robertrico/project_byte_hamr/docs/blog/multiverse/gliders.png

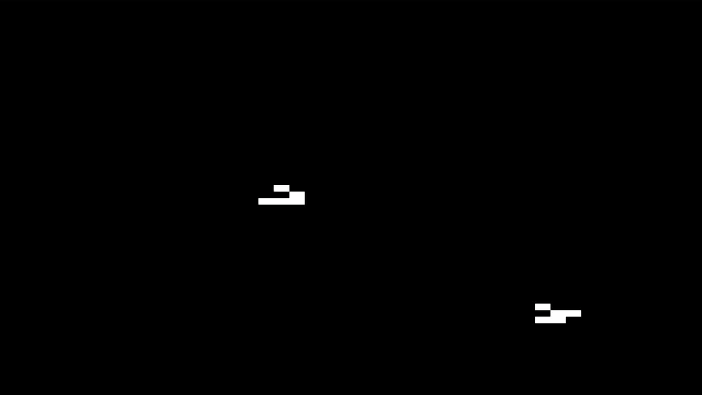
docs/blog/multiverse/gliders.png
