robertrico/project_byte_hamr/docs/blog/multiverse/hero.png

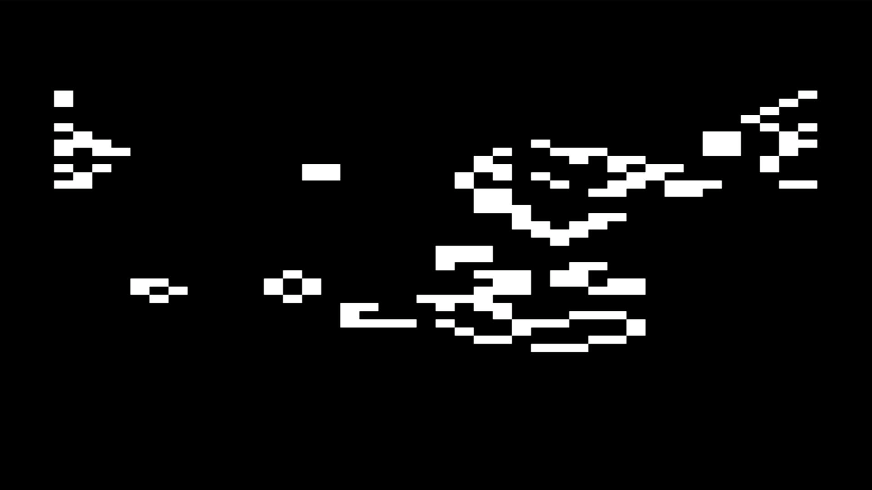
docs/blog/multiverse/hero.png
