robertrico/project_byte_hamr/docs/blog/multiverse/rpentomino-ash.png

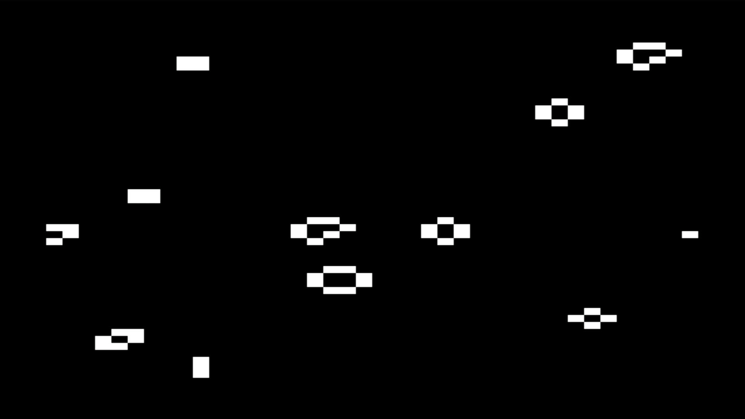
docs/blog/multiverse/rpentomino-ash.png
