robertrico/project_byte_hamr/docs/blog/multiverse/soup-growing.png

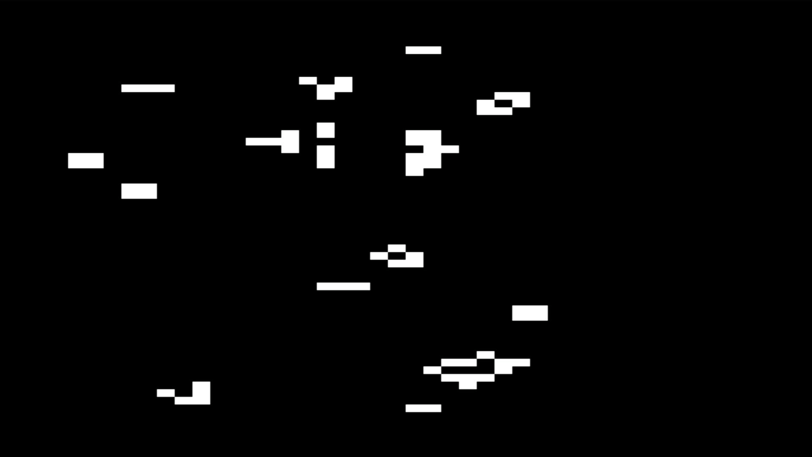
docs/blog/multiverse/soup-growing.png
