robertrico/project_byte_hamr/docs/Logic Hamr/Screenshot 2026-02-04 16-10-01.png

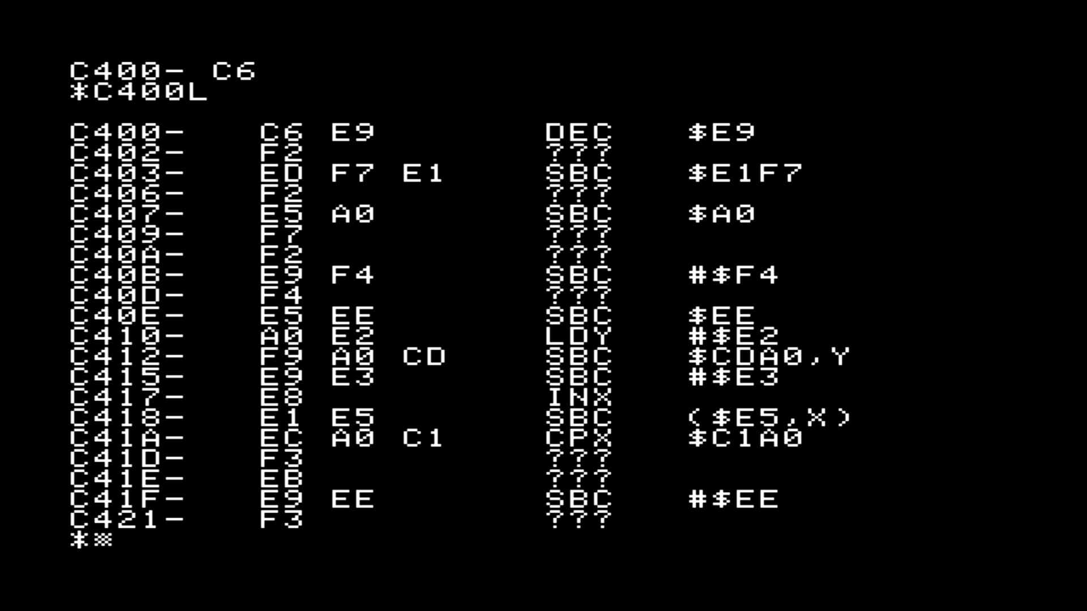
docs/Logic Hamr/Screenshot 2026-02-04 16-10-01.png
