robertrico/project_byte_hamr/docs/Logic Hamr/Screenshot 2026-02-04 16-26-15.png

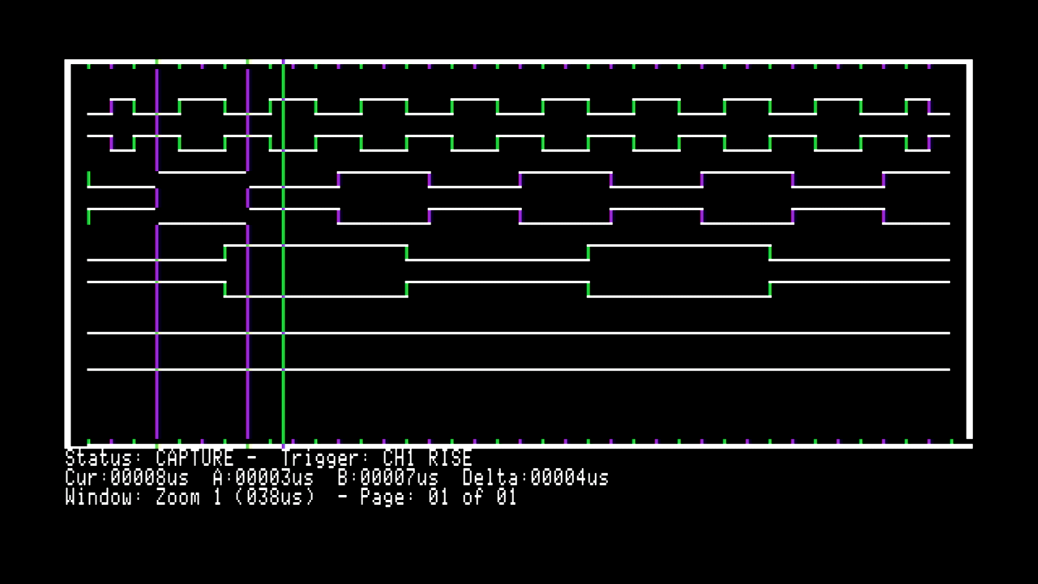
docs/Logic Hamr/Screenshot 2026-02-04 16-26-15.png
