robertrico/project_byte_hamr/docs/Logic Hamr/Screenshot 2026-02-04 16-27-03.png

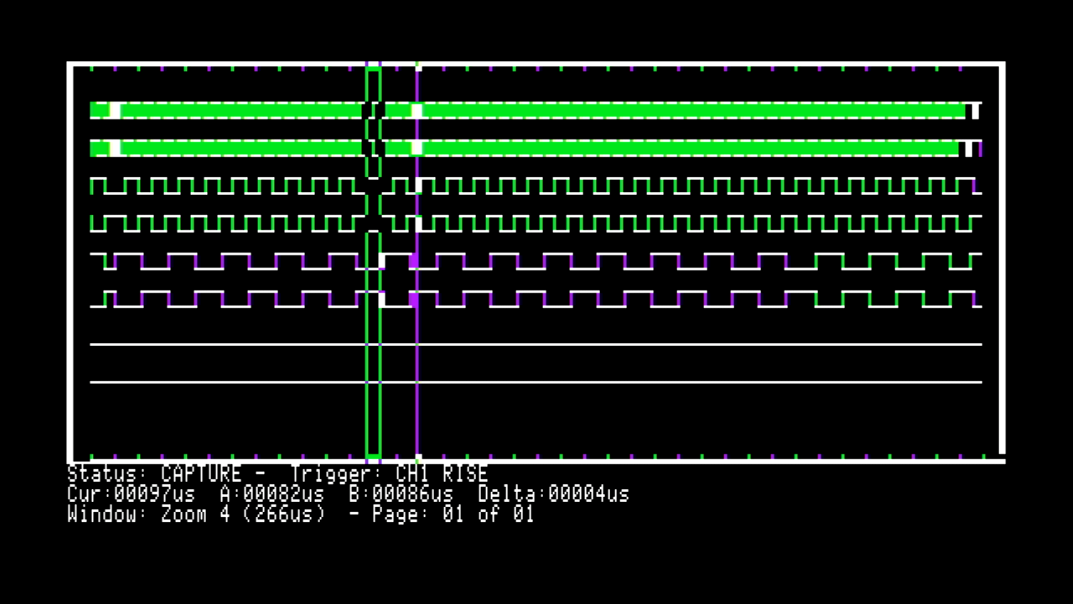
docs/Logic Hamr/Screenshot 2026-02-04 16-27-03.png
