robertrico/project_byte_hamr/docs/Logic Hamr/Screenshot 2026-02-04 17-45-49.png

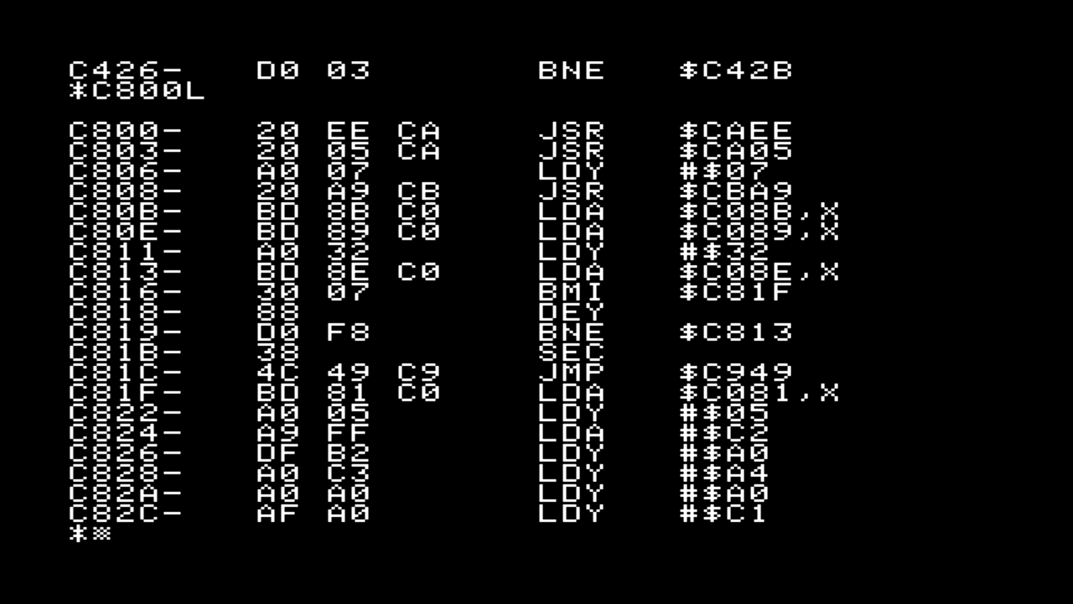
docs/Logic Hamr/Screenshot 2026-02-04 17-45-49.png
