robertrico/project_byte_hamr/docs/Logic Hamr/Screenshot 2026-02-07 22-06-17.png

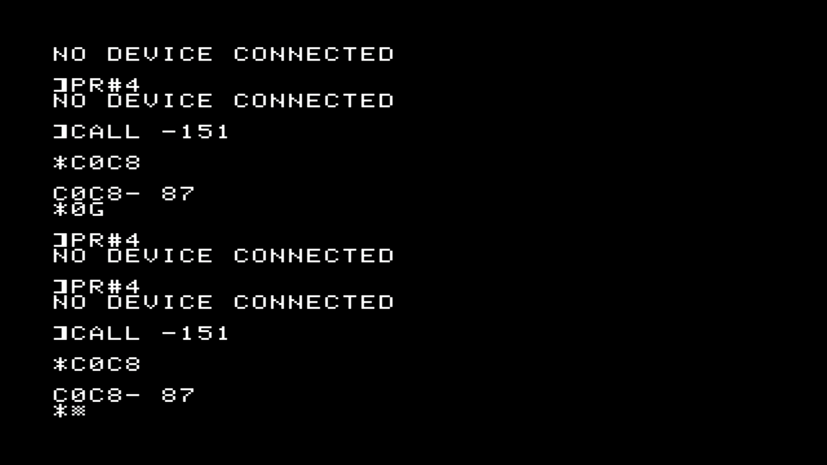
docs/Logic Hamr/Screenshot 2026-02-07 22-06-17.png
