robertrico/project_byte_hamr/docs/Logic Hamr/Screenshot 2026-02-08 11-18-13.png

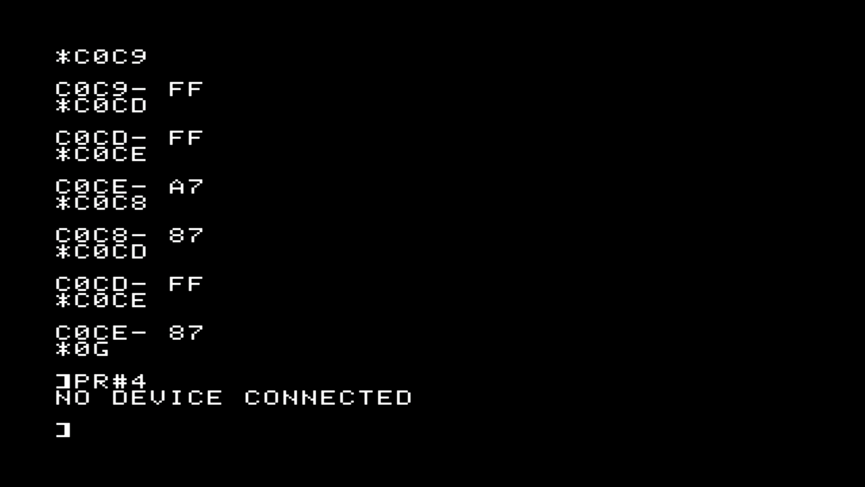
docs/Logic Hamr/Screenshot 2026-02-08 11-18-13.png
