robertrico/project_byte_hamr/docs/project_byte_hamr.jpg

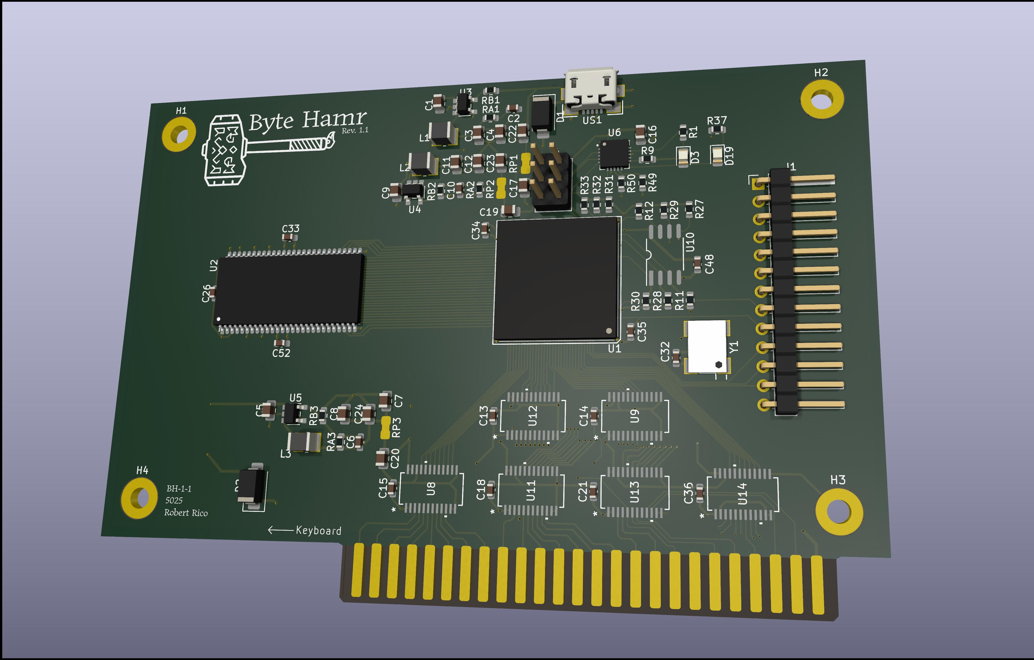
docs/project_byte_hamr.jpg
