robertrico/project_byte_hamr/docs/project_byte_hamr_back.jpg

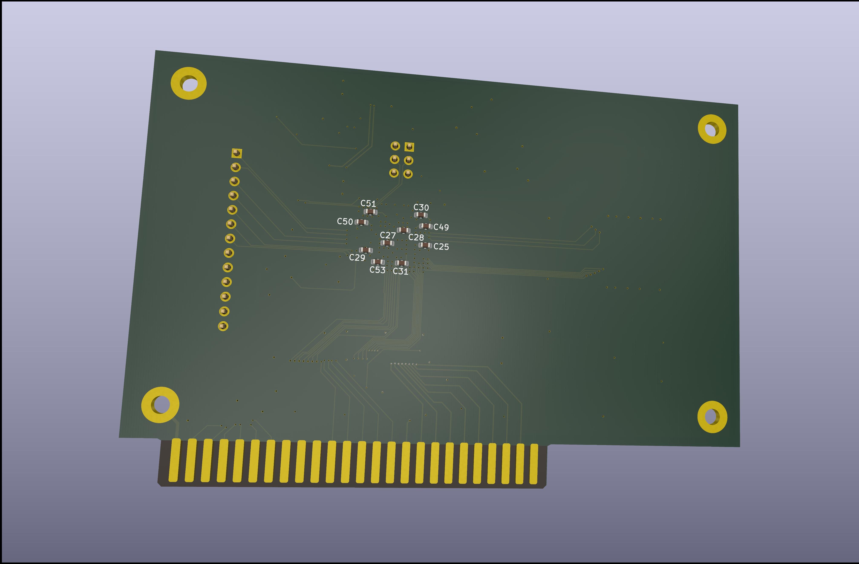
docs/project_byte_hamr_back.jpg
