robertrico/project_byte_hamr/docs/Smart Hamr/Screenshot 2026-03-02 16-48-08.png

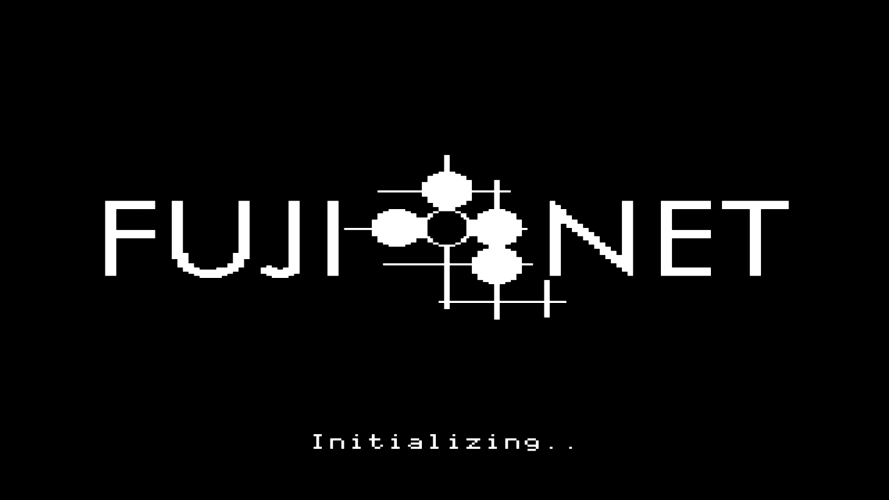
docs/Smart Hamr/Screenshot 2026-03-02 16-48-08.png
