robertrico/project_byte_hamr/docs/Smart Hamr/Screenshot 2026-03-02 16-52-01.png

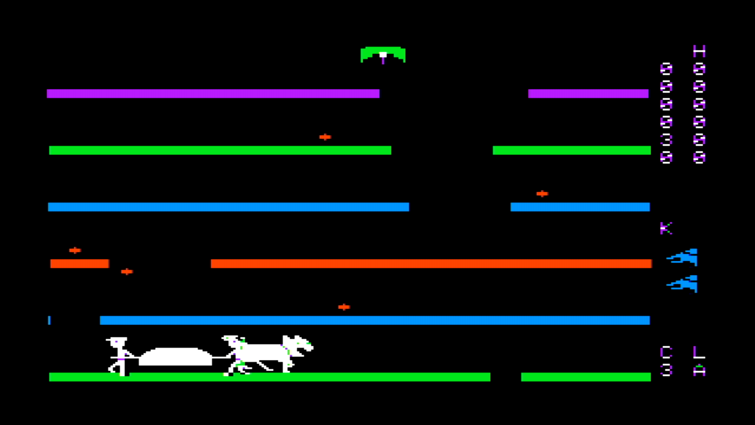
docs/Smart Hamr/Screenshot 2026-03-02 16-52-01.png
