robertrico/project_byte_hamr/docs/Smart Hamr/Screenshot 2026-03-02 16-53-50.png

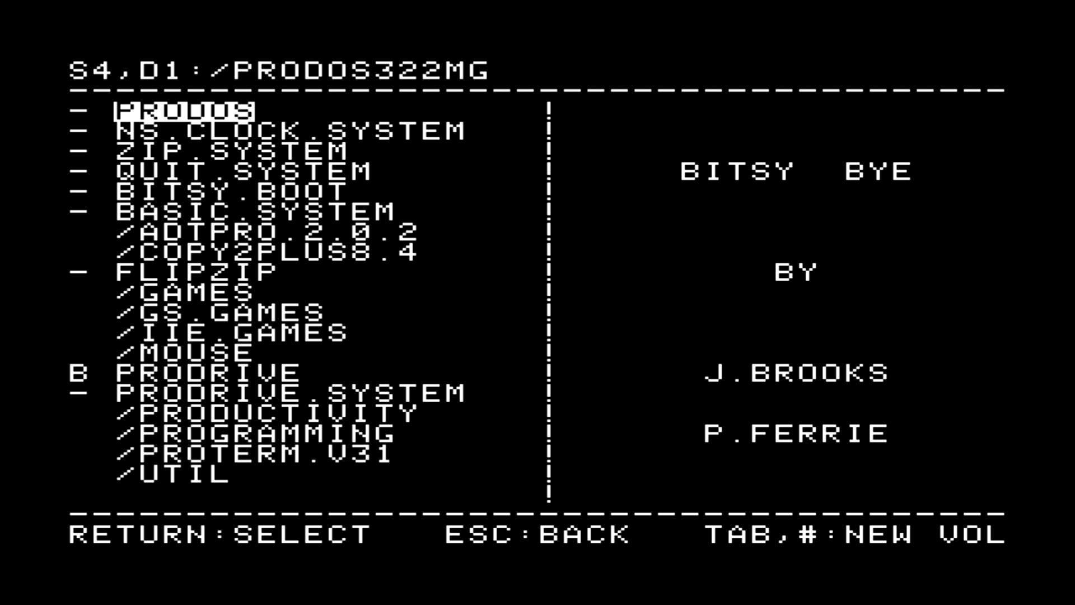
docs/Smart Hamr/Screenshot 2026-03-02 16-53-50.png
