robertrico/project_byte_hamr/docs/Smart Hamr/Screenshot 2026-03-02 17-01-03.png

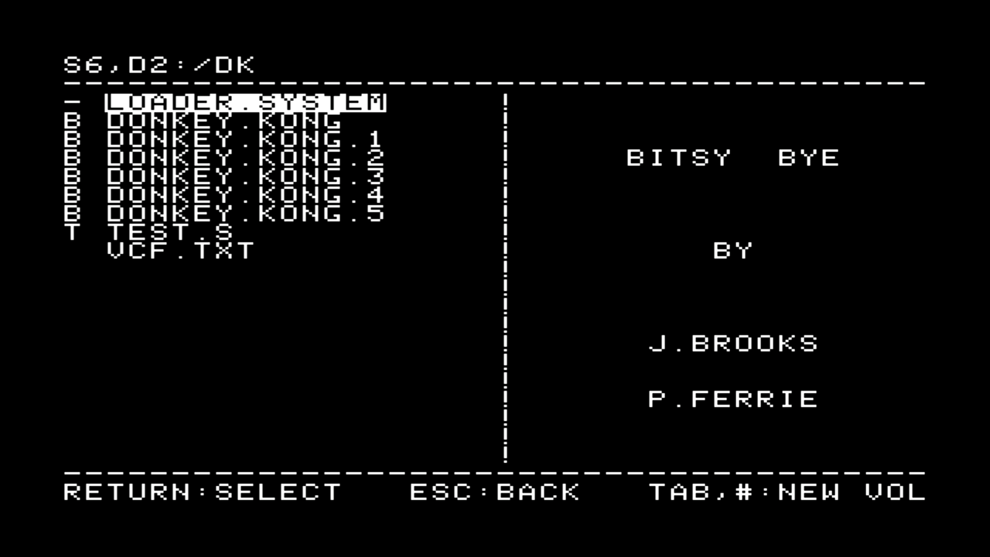
docs/Smart Hamr/Screenshot 2026-03-02 17-01-03.png
