robertrico/project_byte_hamr/docs/Smart Hamr/Screenshot 2026-03-02 17-02-29.png

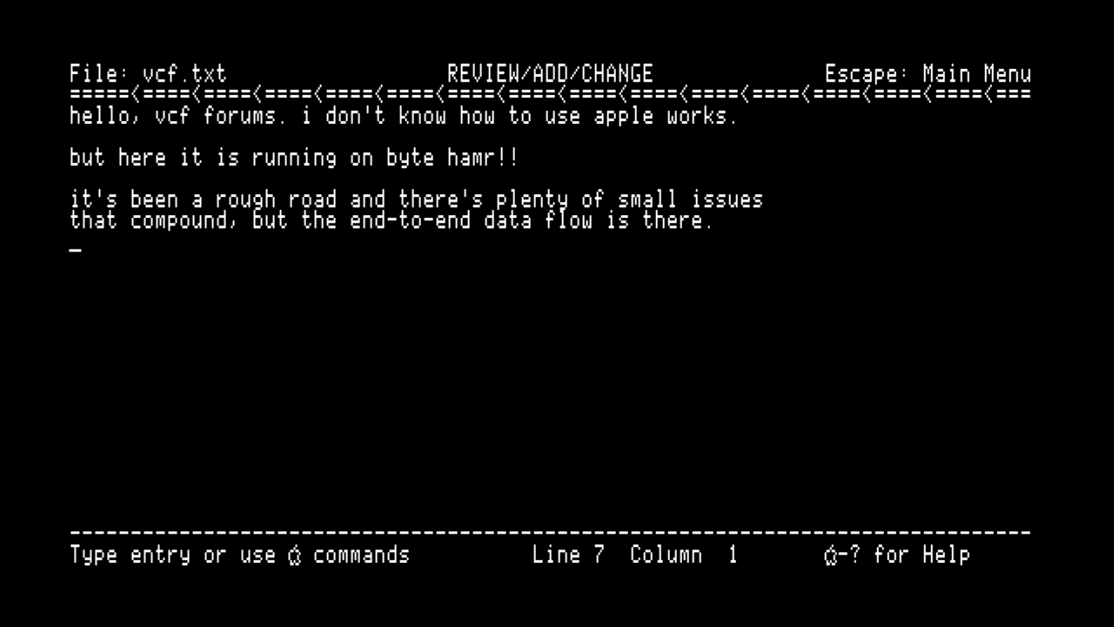
docs/Smart Hamr/Screenshot 2026-03-02 17-02-29.png
