robertrico/project_byte_hamr/docs/timing_chart.jpg

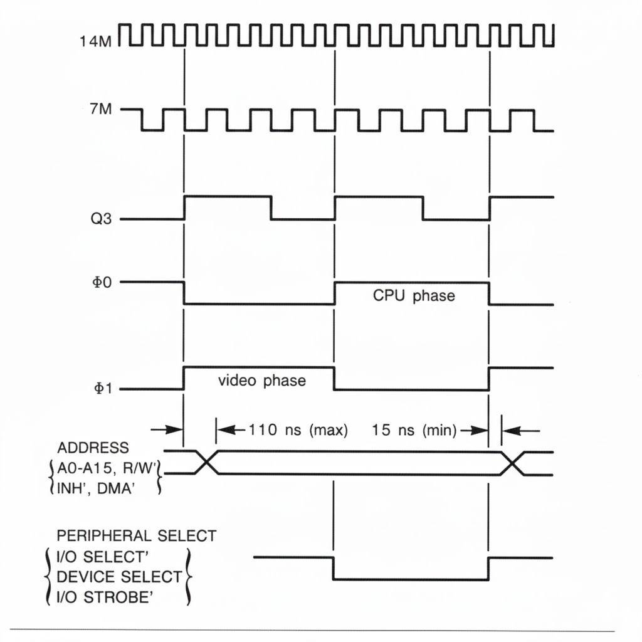
docs/timing_chart.jpg
