robertrico/project_byte_hamr/gateware/rev2/block_hamr/hamr_rom.asm

; =============================================================================
; hamr_rom.asm — Byte Hamr ProDOS/SmartPort block device ROM
; =============================================================================
; Talks to FPGA register file for block reads/writes.
;
; Register interface ($C0n0 + slot*16):
;   REG_CMD   ($C080,X): Read = STATUS, Write = COMMAND
;     STATUS read:  {ready, error, 5'b0, boot_done}
;     COMMAND write: $01 = READ_BLOCK, $02 = WRITE_BLOCK
;   REG_DATA  ($C081,X): Read/Write data, auto-increments
;   REG_BLK_LO ($C082,X): Block number low byte
;   REG_BLK_HI ($C083,X): Block number high byte
;
; ROM memory map (as seen by boot_rom.v):
;   $400-$4FF: Slot ROM ($Cn00-$CnFF)
;   $800-$FFF: Shared ROM ($C800-$CFFF)
;
; Assembled for slot 4, but slot number only matters for the $Cn
; page — the $C800 code uses dynamic slot detection.
; =============================================================================

	cpu	65c02

; ---- Zero page temporaries (safe range $40-$5B) ----
slot		equ	$58	; slot number (1-7)
buf_ptr		equ	$44	; ProDOS buffer pointer (lo/hi)
buf_ptr_h	equ	$45

; ---- ProDOS command block ($42-$47) ----
prodos_command	equ	$42
prodos_unit	equ	$43
prodos_buffer	equ	$44
prodos_block	equ	$46
prodos_block_h	equ	$47

; ---- Screen holes (per-slot, indexed by slot number) ----
sh_prodos_flag	equ	$0478	; MSB=1 for ProDOS, 0 for SmartPort
sh_magic1	equ	$06f8	; $A5 if initialized
sh_magic2	equ	$0778	; $5A if initialized
sh_unit_count	equ	$07f8	; number of units
sh_05f8		equ	$05f8	; SmartPort return addr lo
sh_0678		equ	$0678	; SmartPort return addr hi

; ---- Global screen holes ----
gh_shared_slot	equ	$07f8	; $Cn for active $C800 ROM

; ---- Apple II ROM / Monitor ----
rom_dis		equ	$cfff	; accessing this deactivates $C800 ROMs

; ---- I/O register base addresses (indexed by slot*16) ----
REG_CMD		equ	$c080	; STATUS read / COMMAND write
REG_DATA	equ	$c081	; DATA (auto-increment)
REG_BLK_LO	equ	$c082	; Block number low
REG_BLK_HI	equ	$c083	; Block number high

; ---- ProDOS error codes ----
ERR_NONE	equ	$00
ERR_BAD_CMD	equ	$01
ERR_IO		equ	$27
ERR_NO_DRIVE	equ	$28
ERR_NO_WRITE	equ	$2b
ERR_BAD_BLOCK	equ	$2d

; ---- Block count for .po image (280 blocks = $0118) ----
BLOCK_COUNT_LO	equ	$18	; 280 & $FF
BLOCK_COUNT_HI	equ	$01	; 280 >> 8

; ---- Commands ----
CMD_READ	equ	$01
CMD_WRITE	equ	$02


; =============================================================================
; Slot ROM: $C400-$C4FF (mapped to ROM $400-$4FF)
; =============================================================================
; ProDOS looks for: $Cn01=$20, $Cn03=$00, $Cn05=$03, $CnFF=entry_lo
; Boot entry is at $Cn00 with carry set (from boot scan)

	org	$c400

; ---- Boot/signature entry ($C400 = $Cn00) ----
	ldx	#$20		; $Cn01 = $20: block device
	ldx	#$00		; $Cn03 = $00: no specific type
	ldx	#$03		; $Cn05 = $03: "smart" device (supports STATUS)
	cmp	#$00		; $Cn07 = $00 (padding)
	bcs	cn14		; carry set = boot request

; ---- ProDOS entry ($C409 = $Cn09) ----
prodos_entry:
	sec
	bcs	cn0e

; ---- SmartPort entry ($C40B = $Cn0B) ----
smartport_entry:
	clc

; ---- Combined dispatch ($C40C = $Cn0E, after CLC/SEC) ----
cn0e:
	ldx	#$04		; slot 4
	ror	sh_prodos_flag,x
	clc			; clear carry for execute_command path

; ---- Combined boot/command entry ($C414 = $Cn14) ----
cn14:
	ldx	#$c4		; $C0 + slot
	stx	gh_shared_slot
	ldx	#$04		; slot number
	lda	rom_dis		; deactivate other $C800 ROMs
	jmp	shared_entry	; jump to $C800 space

; ---- Pad to $CnFB ----
	; (filler — rest of $Cn space available for future use)

	org	$c4fb

	fcb	$00		; $CnFB: SmartPort device type (0 = block device)
	fdb	$0000		; $CnFC-FD: block count (0 = requires STATUS call)
	fcb	$bf		; $CnFE: ProDOS characteristics
				;   bit 7: removable
				;   bit 5: support STATUS
				;   bit 4: support READ/WRITE
				;   bit 3: support FORMAT
				;   bit 0: support SmartPort
	fcb	prodos_entry & $ff  ; $CnFF: ProDOS entry point low byte


; =============================================================================
; Shared ROM: $C800-$CFFF (mapped to ROM $800-$FFF)
; =============================================================================

	org	$c800

; ---- Entry point from slot ROM ----
shared_entry:
	bcc	execute_command	; C=0: ProDOS/SmartPort command
	jmp	boot		; C=1: boot request

; ---- Command dispatcher ----
execute_command:
	cld
	stx	slot		; save slot number

	; Get slot*16 into X for register access
	jsr	get_slot_x

	lda	sh_prodos_flag-1,x	; wait — X is slot*16 here, not slot
	; Fix: need slot number for screen hole indexing
	; Screen holes are indexed by slot number, not slot*16

	; Reload slot number for screen hole access
	ldy	slot

	lda	sh_prodos_flag,y
	bmi	prodos_cmd	; MSB=1: ProDOS call

	; ---- SmartPort call ----
	; Pull return address from stack, read inline params
	pla
	sta	sh_05f8,y	; return addr lo
	clc
	adc	#$03		; skip cmd byte + param ptr
	tax
	pla
	sta	sh_0678,y	; return addr hi
	adc	#$00
	pha			; push adjusted return addr
	txa
	pha

	; Read SmartPort command byte and param list from inline data
	lda	sh_05f8,y
	sta	buf_ptr
	lda	sh_0678,y
	sta	buf_ptr_h

	ldy	#$01
	lda	(buf_ptr),y	; SmartPort command
	sta	prodos_command
	iny
	lda	(buf_ptr),y	; param list lo
	tax
	iny
	lda	(buf_ptr),y	; param list hi
	sta	buf_ptr_h
	stx	buf_ptr

	; Copy SmartPort params to ProDOS command block
	ldy	#$00
	lda	(buf_ptr),y	; param count (ignored for now)
	iny
	lda	(buf_ptr),y	; unit number
	sta	prodos_unit
	iny
	lda	(buf_ptr),y	; buffer lo
	sta	prodos_buffer
	iny
	lda	(buf_ptr),y	; buffer hi
	sta	prodos_buffer+1
	iny
	lda	(buf_ptr),y	; block lo
	sta	prodos_block
	iny
	lda	(buf_ptr),y	; block hi
	sta	prodos_block_h

	; Fall through to ProDOS dispatch

prodos_cmd:
	jsr	get_slot_x	; X = slot*16 for register access

	lda	prodos_command
	beq	cmd_status
	cmp	#$01
	beq	cmd_read
	cmp	#$02
	beq	cmd_write
	cmp	#$05
	beq	cmd_init

	; Unknown command
	lda	#ERR_BAD_CMD
	sec
	jmp	cmd_done


; =========================================================================
; STATUS (command $00)
; =========================================================================
; Returns: X = block count lo, Y = block count hi
;          A = 0 (no error)

cmd_status:
	; Check if device is ready
	lda	REG_CMD,x
	and	#$01		; boot_done?
	beq	status_offline

	lda	#$f8		; status: online, block device, read/write, format
	ldx	#BLOCK_COUNT_LO
	ldy	#BLOCK_COUNT_HI
	lda	#ERR_NONE
	clc
	jmp	cmd_done

status_offline:
	lda	#ERR_NO_DRIVE
	sec
	jmp	cmd_done


; =========================================================================
; READ BLOCK (command $01)
; =========================================================================
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
